sidfi/sidfi/firmware/sidfi.X/gfx.h

#ifndef __GFX_H__
#define __GFX_H__

#ifdef __cplusplus
extern "C" {
#endif

void setPixel(uint16_t, uint16_t);
/* background pixel used for font draw */
void setbgPixel(uint16_t, uint16_t);
void fillScreen(void);
/* needs to be the last action when using BUFFER or HVBUFFER */
void flushBuffer(void);
void setFont(const uint8_t *);
void drawText(uint16_t, uint16_t, const char *);
void drawCircle(uint16_t, uint16_t, uint16_t);
void filledCircle(uint16_t, uint16_t, uint16_t);
void drawArc(uint16_t, uint16_t, uint16_t, float, float);
void drawPie(uint16_t, uint16_t, uint16_t, float, float);
void drawLine(uint16_t,uint16_t, uint16_t, uint16_t);
void setColorRaw(color565_t);
void setbgColorRaw(color565_t);
void setColor(uint8_t, uint8_t, uint8_t);
void setTransparent(bool);
/* background color for fonts if !transparent */
void setbgColor(uint8_t, uint8_t, uint8_t);
void drawRect(uint16_t, uint16_t, uint16_t, uint16_t);
void filledRect(uint16_t, uint16_t, uint16_t, uint16_t);
void setColor24(uint32_t);
void setbgColor24(uint32_t);

#ifdef __cplusplus
} // extern "C"
#endif

#endif
